zimmer62/Lumary-ESPHome/hardware/kicad/CBU-Drop-in/LearningTest2.kicad_sch

## KiCad design hardware/kicad/CBU-Drop-in/LearningTest2.kicad_sch (2026-01-01)

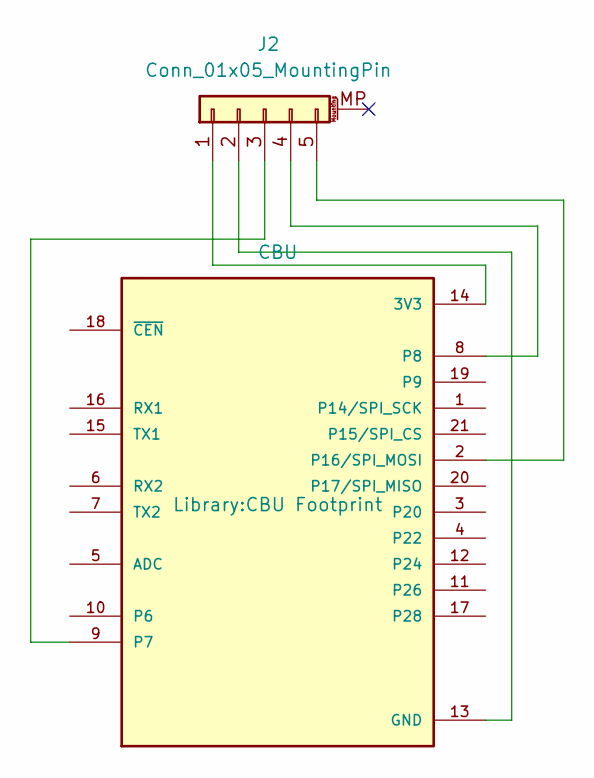
[picture p9: schematic LearningTest2.kicad_sch]

Parts:
J2: Conn_01x05_MountingPin; JST_GH_SM05B-GHS-TB_1x05-1MP_P1.25mm_Horizontal
U1: CBU; CBU Footprint; PARTREV 2023-05-16

Connections:
unnamed: J2.1, U1.14 (3V3)
unnamed: J2.2, U1.13 (GND)
unnamed: J2.3, U1.9 (P7)
unnamed: J2.4, U1.8
unnamed: J2.5, U1.2 (P16/SPI_MOSI)
