zimmer62/Lumary-ESPHome/hardware/kicad/CBU-Replacement-Daughterboard/CBU-Replacement-Daughterboard.kicad_sch

## KiCad design hardware/kicad/CBU-Replacement-Daughterboard/CBU-Replacement-Daughterboard.kicad_sch (2026-01-01)

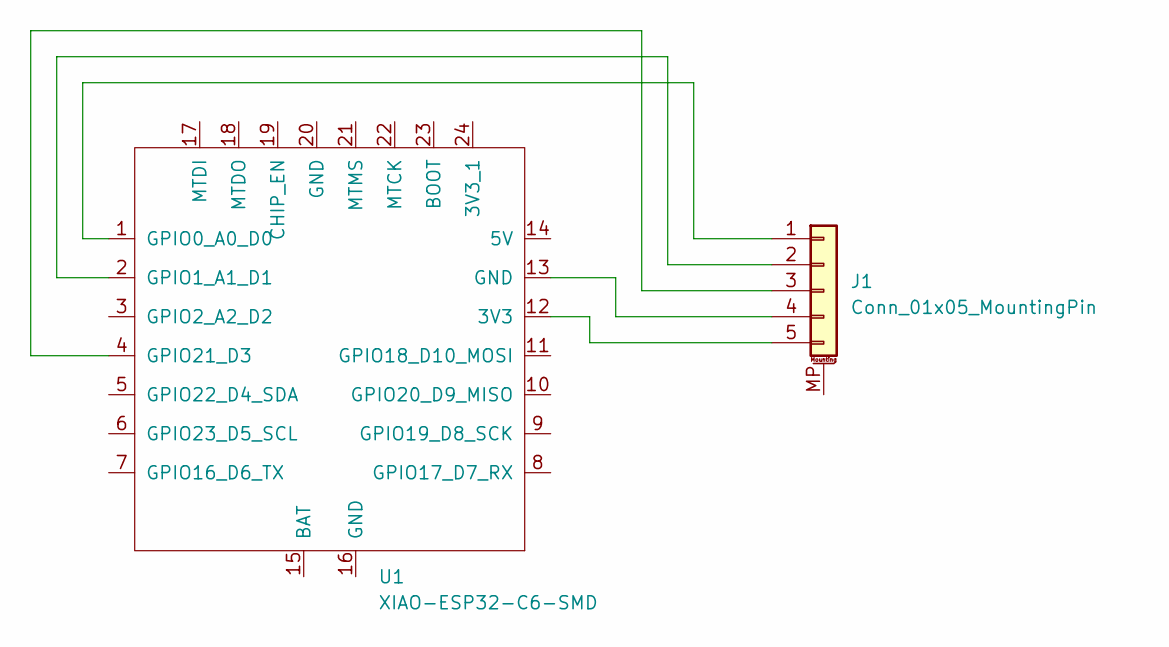
[picture p10: schematic CBU-Replacement-Daughterboard.kicad_sch]

Parts:
J1: Conn_01x05_MountingPin; JST_GH_SM05B-GHS-TB_1x05-1MP_P1.25mm_Horizontal
U1: XIAO-ESP32-C6-SMD; XIAO-ESP32C6-SMD

Connections:
unnamed: J1.1, U1.1 (GPIO0_A0_D0)
unnamed: J1.2, U1.2 (GPIO1_A1_D1)
unnamed: J1.3, U1.4 (GPIO21_D3)
unnamed: J1.4, U1.13 (GND)
unnamed: J1.5, U1.12 (3V3)
